tompi/cheapino/doc/gallery/crimper.jpg

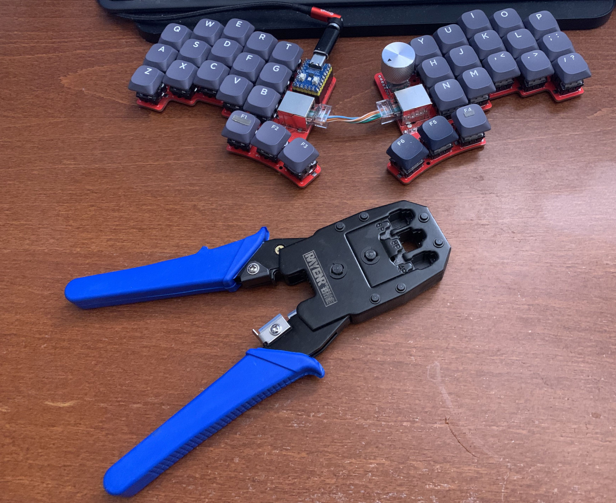
doc/gallery/crimper.jpg
