tompi/cheapino/doc/gallery/v1/cheapino.jpg

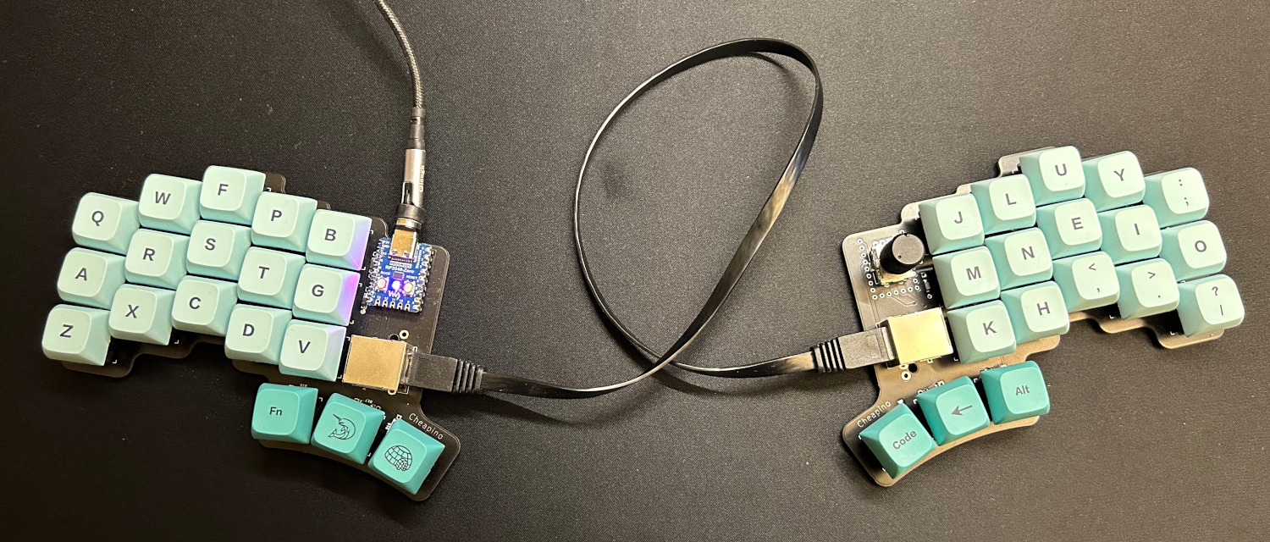
doc/gallery/v1/cheapino.jpg
