tompi/cheapino/doc/images/bodge2.png

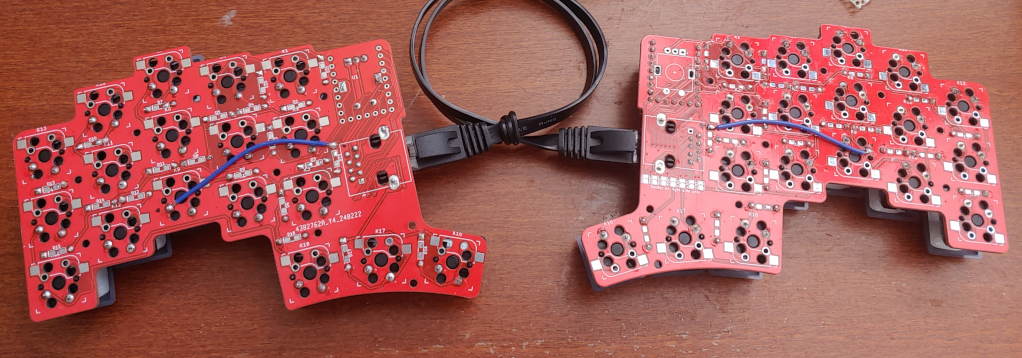
doc/images/bodge2.png
