tompi/cheapino/doc/images/bodge.png

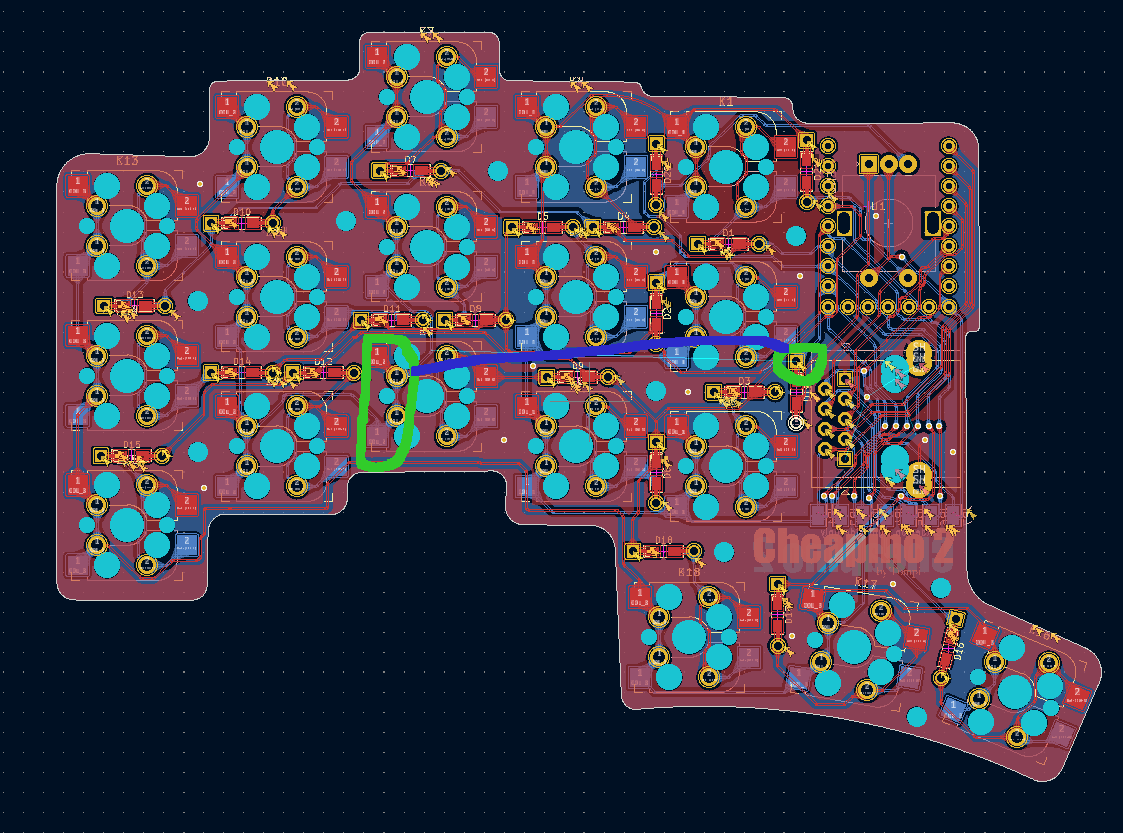
doc/images/bodge.png
