tompi/cheapino/doc/images/diodes.jpeg

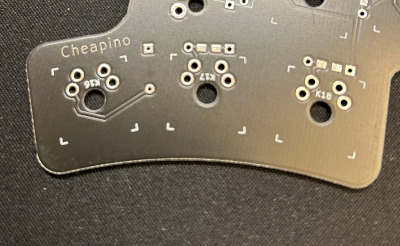
doc/images/diodes.jpeg
