tompi/cheapino/plates/openscad_wip/cheapino.scad

height = 95.1738;
width = 132.6134;
$fn=30;

height_translation = 0;

// Height of case is 5mm from pcb to switch inset,
// plus 1.6mm pcb height, for a total of 6.6mm
for (i = [0:0.05:2.5])
{
    translate([0,0,i]) //height_translation])
        base_line_extruded(i, 0.1);
}

translate([0,0,2.5]) //height_translation])
  base_line_extruded(2.5, 1.6);

for (i = [4.1b:0.05:6.6])
{
    translate([0,0,i]) //height_translation])
        base_line_extruded(6.6-i, 1);
}


module base_line_extruded (factor, extrusion)
{
    linear_extrude(extrusion)
            base_line(factor);
}

module base_extended (factor, extrusion)
{
    linear_extrude(extrusion)
        offset( delta=factor)
            base();
}

module base()
{
	import ("base.svg", center=true);
}


module base_line(expanded)
{
  difference()
  {
    offset( delta=expanded+1)
            base();
    offset( delta=expanded)
            base();
  }
}

/*
module base_extended(factor, extrusion)
{
  linear_extrude(extrusion)
    offset([factor, factor, 1])
      base();
}

module base()
{
  import("base.svg", center=false);
}
*/
